ptbediako/IoTCapstone2025/FDA Screenshot 2025-08-14 154539.jpg

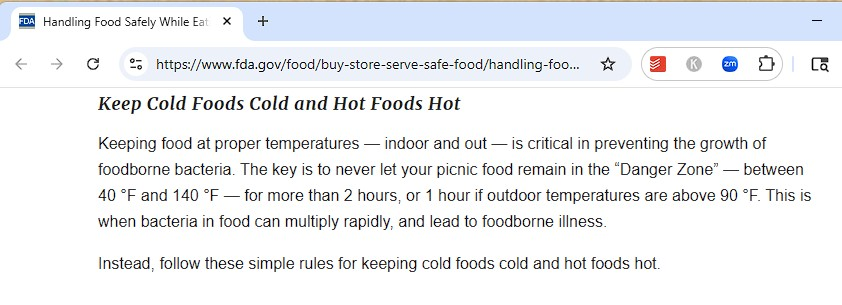
FDA Screenshot 2025-08-14 154539.jpg
