ptbediako/IoTCapstone2025/Sample Dashboard PC Screenshot 2025-08-13 205112.jpg

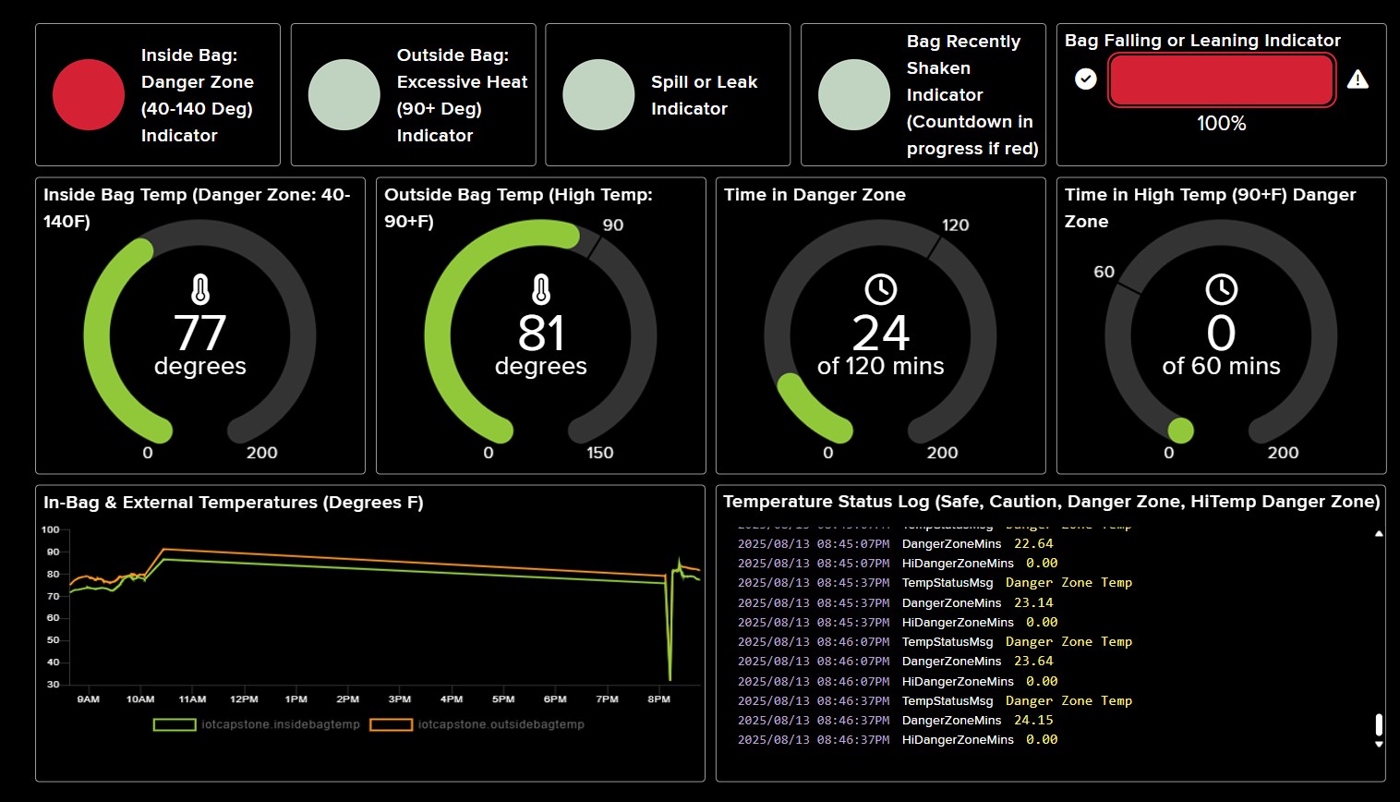
Sample Dashboard PC Screenshot 2025-08-13 205112.jpg
