ptbediako/IoTCapstone2025/USDA Screenshot 2025-08-14 154831.jpg

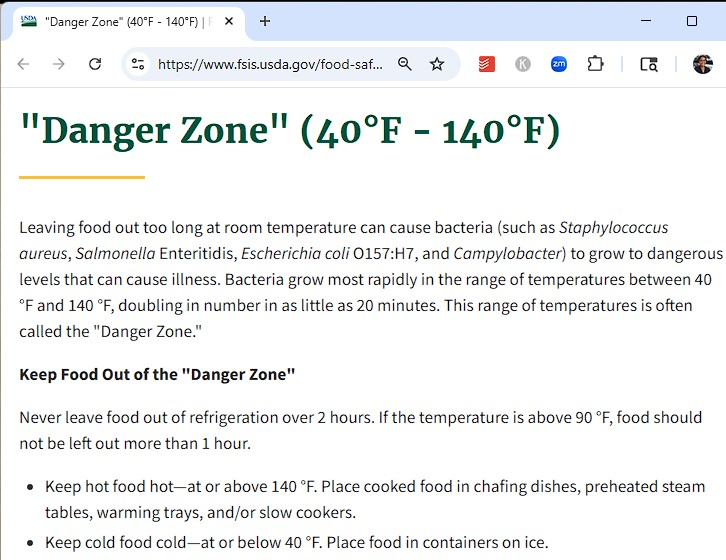
USDA Screenshot 2025-08-14 154831.jpg
