ptbediako/IoTCapstone2025/ZapFallScreenshot 2025-08-14 164707.jpg

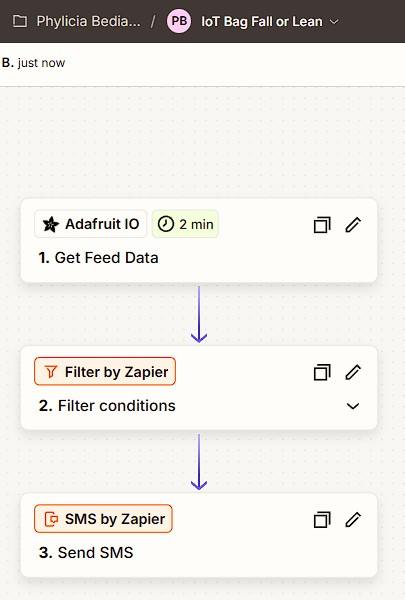
ZapFallScreenshot 2025-08-14 164707.jpg
