ptbediako/IoTCapstone2025/ZapFoodTemp.jpg

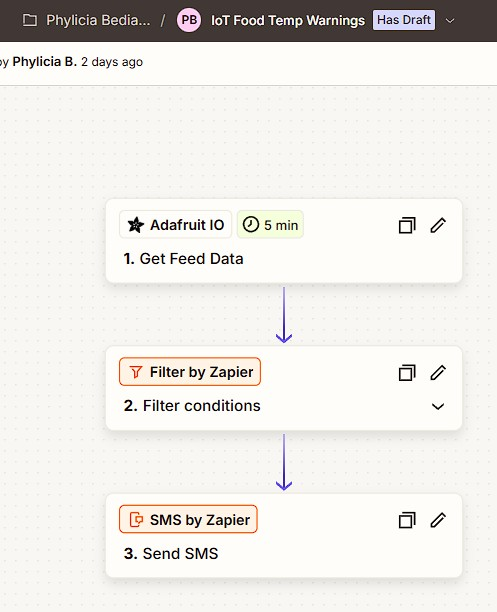
ZapFoodTemp.jpg
