ptbediako/IoTCapstone2025/ZapSpillScreenshot 2025-08-14 164549.jpg

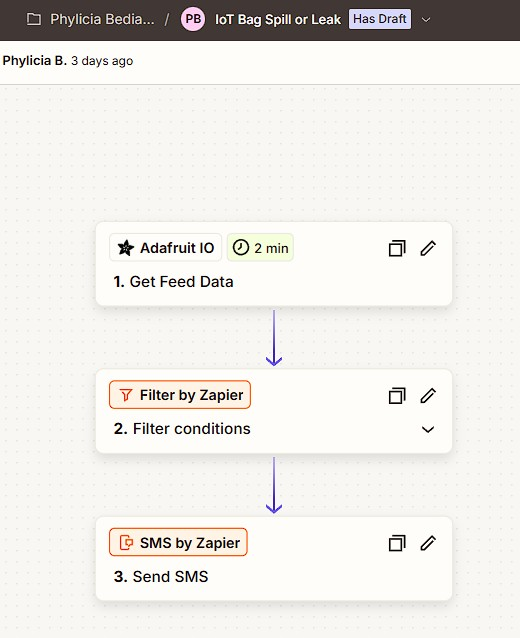
ZapSpillScreenshot 2025-08-14 164549.jpg
