ptbediako/IoTCapstone2025/Zapier Setup Screenshot 2025-08-11 082937.jpg

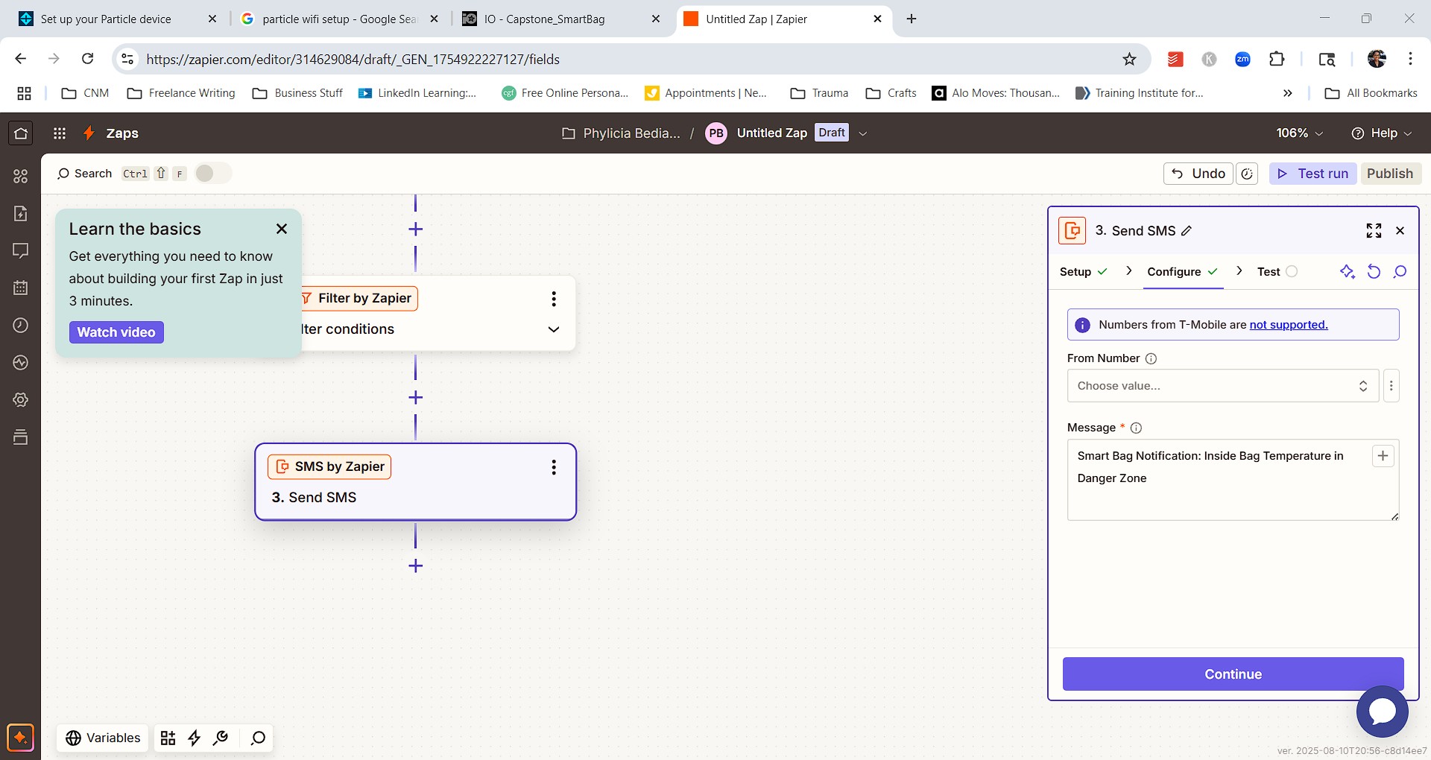
Zapier Setup Screenshot 2025-08-11 082937.jpg
